mossblaser/lineOfLife/physical/base_axel.stl

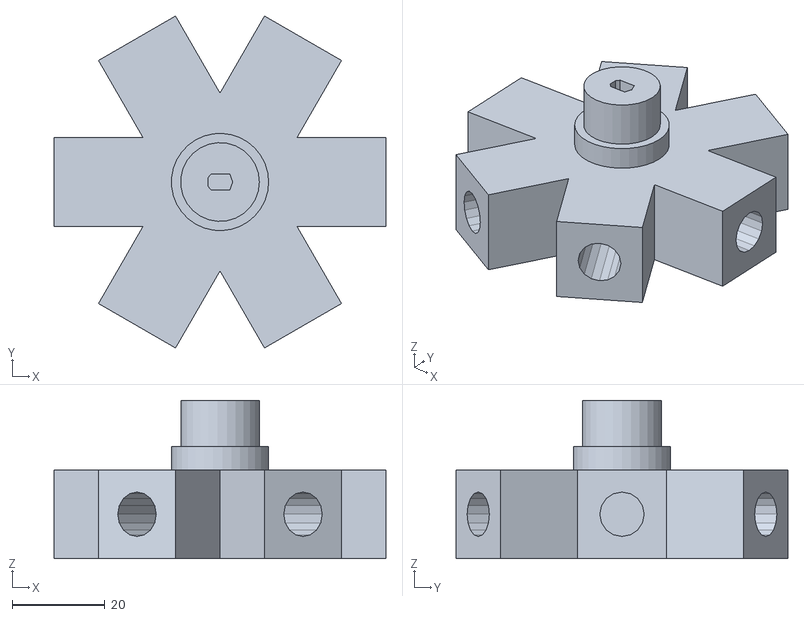
[picture p15: CAD file, 2014-01-31]
physical/base_axel.stl
71.7 x 71.7 x 34.2
