mossblaser/lineOfLife/controller/error_bitmap.h

{0x00,0x00,0x00,0x00,0x00,0x00,0x00,0x00,0x00,0x00,0x00,0x00,0x00,0x00,0x00},
{0x00,0x00,0x00,0x00,0x00,0x00,0x00,0x00,0x00,0x00,0x00,0x00,0x00,0x00,0x00},
{0x00,0x00,0x00,0x00,0x00,0x00,0x00,0x00,0x00,0x00,0x00,0xFC,0xFF,0x3F,0x00},
{0x00,0x00,0x00,0x00,0x00,0x00,0x00,0x00,0x00,0x00,0x00,0xFC,0xFF,0x3F,0x00},
{0x00,0x00,0x00,0x00,0x00,0x00,0x00,0x00,0x00,0x00,0x00,0xFC,0xFF,0x3F,0x00},
{0x00,0x00,0x00,0x00,0x00,0x00,0x00,0x00,0x00,0x00,0x00,0xFC,0xFF,0x3F,0x00},
{0x00,0x80,0xFF,0xFF,0x07,0x00,0x00,0x00,0x00,0x00,0x00,0xFC,0xFF,0x3F,0x00},
{0x00,0x80,0xFF,0xFF,0x07,0x00,0x00,0x00,0x00,0x00,0x00,0x3C,0x00,0x00,0x00},
{0x00,0x80,0xFF,0xFF,0x07,0x00,0x00,0x00,0x00,0x00,0x00,0x3C,0x00,0x00,0x00},
{0x00,0x80,0xFF,0xFF,0x07,0x00,0x00,0x00,0x00,0x00,0x00,0x3C,0x00,0x00,0x00},
{0x00,0x80,0xFF,0xFF,0x07,0x00,0x00,0x00,0x00,0x00,0x00,0x3C,0x00,0x00,0x00},
{0x00,0x80,0x07,0x00,0x00,0x00,0x00,0x00,0x00,0x00,0x00,0x3C,0x00,0x00,0x00},
{0x00,0x80,0x07,0x00,0x00,0x00,0x00,0x00,0x00,0x00,0x00,0x3C,0x00,0x00,0x00},
{0x00,0x80,0x07,0x00,0x00,0x00,0x00,0x00,0x00,0x00,0x00,0x3C,0x00,0x00,0x00},
{0x00,0x80,0x07,0x00,0x00,0x00,0x00,0x00,0x00,0x00,0x00,0x3C,0x00,0x00,0x00},
{0x00,0x80,0x07,0x00,0x00,0x00,0x00,0x00,0x00,0x00,0x00,0x00,0x00,0x00,0x00},
{0x00,0x80,0x07,0x00,0x00,0x00,0x00,0x3C,0x00,0x00,0x00,0x00,0x00,0x00,0x00},
{0x00,0x80,0x07,0x00,0x00,0x00,0x80,0xFF,0x00,0x00,0x00,0x00,0x00,0x00,0x00},
{0x00,0x80,0x07,0x00,0x00,0x00,0xC0,0xFF,0x01,0x00,0x00,0xFC,0xFF,0x38,0x00},
{0x00,0x00,0x00,0x00,0x00,0x00,0xE0,0xFF,0x03,0x00,0x00,0xFC,0xFF,0x7C,0x00},
{0x00,0x00,0x00,0x00,0x00,0x00,0xE0,0xFF,0x07,0x00,0x00,0xFC,0xFF,0x7C,0x00},
{0x00,0x80,0xFF,0x1F,0x02,0x00,0xE0,0x81,0x07,0x00,0x00,0xFC,0xFF,0x38,0x00},
{0x00,0x80,0xFF,0x3F,0x0F,0x00,0xF0,0x00,0x07,0x00,0x00,0x00,0x00,0x00,0x00},
{0x00,0x80,0xFF,0x3F,0x0F,0x00,0xF0,0x00,0x07,0x00,0x00,0x00,0x00,0x00,0x00},
{0x00,0x80,0xFF,0x3F,0x0F,0x00,0xF0,0x00,0x07,0x00,0x00,0x00,0x00,0x00,0x00},
{0x00,0x80,0xFF,0x3F,0x07,0x00,0xF0,0x00,0x07,0x00,0x00,0x00,0x00,0x00,0x00},
{0x00,0x00,0x00,0x00,0x00,0x00,0xE0,0xE7,0x07,0x00,0x00,0xFC,0xFF,0x00,0x00},
{0x00,0x00,0x00,0x00,0x00,0x00,0xE0,0xFF,0x07,0x00,0x00,0xFC,0xFF,0x00,0x00},
{0x00,0x00,0x00,0x3C,0x00,0x00,0xC0,0xFF,0x03,0x00,0x00,0xFC,0xFF,0x00,0x00},
{0x00,0x00,0x00,0x3C,0x00,0x00,0x80,0xFF,0x01,0x00,0x00,0xFC,0xFF,0x00,0x00},
{0x00,0x80,0xFF,0xFF,0x00,0x00,0x00,0xFF,0x00,0x00,0x00,0x00,0x78,0x00,0x00},
{0x00,0x80,0xFF,0xFF,0x03,0x00,0x00,0x00,0x00,0x00,0x00,0x00,0xF0,0x00,0x00},
{0x00,0x80,0xFF,0xFF,0x07,0x00,0x00,0x00,0x00,0x00,0x00,0x00,0xE0,0x00,0x00},
{0x00,0x80,0xFF,0xFF,0x0F,0x00,0x00,0x00,0x07,0x00,0x00,0x00,0xE0,0x00,0x00},
{0x00,0x80,0xFF,0xFF,0x0F,0x00,0x00,0x00,0x07,0x00,0x00,0x00,0xF0,0x01,0x00},
{0x00,0x00,0x00,0x3C,0x1F,0x00,0xF0,0xFF,0x7F,0x00,0x00,0xFC,0xFF,0x01,0x00},
{0x00,0x00,0x00,0x3C,0x1E,0x00,0xF0,0xFF,0xFF,0x00,0x00,0xFC,0xFF,0x00,0x00},
{0x00,0x00,0x00,0x18,0x0E,0x00,0xF0,0xFF,0xFF,0x01,0x00,0xFC,0xFF,0x00,0x00},
{0x00,0x00,0x00,0x00,0x00,0x00,0xF0,0xFF,0xFF,0x03,0x00,0xFC,0x7F,0x00,0x00},
{0x00,0x00,0xF8,0x01,0x00,0x00,0x00,0x80,0xF7,0x03,0x00,0xFC,0x0F,0x00,0x00},
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
