mossblaser/lineOfLife/controller/number_bitmaps.h

{
	0x1C, //   111   
	0x22, //  1   1  
	0x32, //  1  11  
	0x2A, //  1 1 1  
	0x26, //  11  1  
	0x22, //  1   1  
	0x1C, //   111   
	0x00, //         
},
{
	0x08, //    1    
	0x0C, //   11    
	0x08, //    1    
	0x08, //    1    
	0x08, //    1    
	0x08, //    1    
	0x1C, //   111   
	0x00, //         
},
{
	0x1C, //   111   
	0x22, //  1   1  
	0x20, //      1  
	0x10, //     1   
	0x08, //    1    
	0x04, //   1     
	0x3E, //  11111  
	0x00, //         
},
{
	0x3E, //  11111  
	0x10, //     1   
	0x08, //    1    
	0x10, //     1   
	0x20, //      1  
	0x22, //  1   1  
	0x1C, //   111   
	0x00, //         
},
{
	0x10, //     1   
	0x18, //    11   
	0x14, //   1 1   
	0x12, //  1  1   
	0x3E, //  11111  
	0x10, //     1   
	0x10, //     1   
	0x00, //         
},
{
	0x3E, //  11111  
	0x02, //  1      
	0x1E, //  1111   
	0x20, //      1  
	0x20, //      1  
	0x22, //  1   1  
	0x1C, //   111   
	0x00, //         
},
{
	0x18, //    11   
	0x04, //   1     
	0x02, //  1      
	0x1E, //  1111   
	0x22, //  1   1  
	0x22, //  1   1  
	0x1C, //   111   
	0x00, //         
},
{
	0x3E, //  11111  
	0x20, //      1  
	0x10, //     1   
	0x08, //    1    
	0x04, //   1     
	0x04, //   1     
	0x04, //   1     
	0x00, //         
},
{
	0x1C, //   111   
	0x22, //  1   1  
	0x22, //  1   1  
	0x1C, //   111   
	0x22, //  1   1  
	0x22, //  1   1  
	0x1C, //   111   
	0x00, //         
},
{
	0x1C, //   111   
	0x22, //  1   1  
	0x22, //  1   1  
	0x3C, //   1111  
	0x20, //      1  
	0x10, //     1   
	0x0C, //   11    
	0x00, //         
},
