mossblaser/lineOfLife/controller/presenting_bitmap.h

0x78,0x00,0x00,0x00,0x00,0x81,0x00,0x3C,0x00,0x00,0x0C,0x00,0x00,0x00,0x00, //    1111                                 1      1          1111                    11                                    
0x88,0x00,0x00,0x00,0x80,0x03,0x00,0x22,0x00,0x00,0x08,0x00,0x00,0x00,0x00, //    1   1                               111               1   1                     1                                    
0x88,0x1A,0xC7,0x73,0x1A,0xC1,0x68,0x22,0xA0,0x89,0x08,0x07,0x00,0x00,0x00, //    1   1 1 11   111   1111  111  1 11   1     11   1 11  1   1       1 11  1   1   1    111                             
0x78,0xA6,0x28,0x88,0x26,0x81,0x98,0x3C,0x60,0x8A,0x88,0x08,0x00,0x00,0x00, //    1111  11  1 1   1 1     1   1 11  1  1      1   11  1  1111       11  1 1   1   1   1   1                            
0x08,0x82,0xCF,0xF9,0x22,0x81,0x88,0x20,0x20,0x88,0x88,0x0F,0x00,0x00,0x00, //    1     1     11111  111  11111 1   1  1      1   1   1     1       1     1   1   1   11111                            
0x08,0x82,0x00,0x0A,0x22,0x89,0x88,0x20,0x20,0xC8,0x88,0x00,0x00,0x00,0x00, //    1     1     1         1 1     1   1  1  1   1   1   1     1       1     1  11   1   1                                
0x08,0x02,0xE7,0x71,0x22,0xC6,0x89,0x1C,0x20,0xB0,0x1C,0x07,0x00,0x00,0x00, //    1     1      111  1111   111  1   1   11   111  1   1  111        1      11 1  111   111                             
0x00,0x00,0x00,0x00,0x00,0x00,0x00,0x00,0x00,0x00,0x00,0x00,0x00,0x00,0x00, //                                                                                                                         
