mossblaser/lineOfLife/python/examples/cellular_automata.py

#!/usr/bin/env python

"""
A quick-and-dirty 1D cellular automata demo. Displays randomly initialised
automata with random rules. If rules are supplied as arguments, the displayed
rules will be selected from the supplied list of rules.

See http://en.wikipedia.org/wiki/Elementary_cellular_automaton for more details
of this class of automata.
"""

import sys
import serial
import random
import time

from line_of_life.driver import LineOfLife
from line_of_life.bitmap import text_to_lol

# Connect to the display
ser = serial.Serial(port = "/dev/ttyUSB0", baudrate = 115200, timeout = 3)
time.sleep(3)
lol = LineOfLife(ser)

# Clear the display's current buffer to start displaying the new automata
# immediately.
lol.clear_buffer()

lol.pixel_aspect_ratio = 1
lol.pixel_duty = 1.0

# A mask for the bits representing the cells of the automata
mask = (1l<<lol.display_height)-1

while True:
	# Pick a random rule to show, or one selected on the command line
	if len(sys.argv) > 1:
		rule = random.choice(map(int, sys.argv[1:]))
	else:
		rule = int(random.random()*0xFF)
	
	# Announce the automata
	for line in text_to_lol("Presenting Rule %d"%rule, lol.display_height, rotate=True):
		lol.push_line(line)
	lol.push_line([0] * lol.display_height)
	
	# Pick randomly between a random initial state and a single seed pixel
	if random.random() < 0.5:
		state = sum(1l<<n for n in range(lol.display_height) if random.random()<0.5)
	else:
		state = 1<<(lol.display_height/2)
	
	# Run this automata for one quarter of a rotation
	for _ in range(lol.display_width/2):
		# Calculate the new automata state
		new_state = 0l
		state <<= 1
		for bit_num in range(1, lol.display_height+1):
			new_state |= ((rule>>((state>>(bit_num-1))&0b111))&1)<<(bit_num-1)
		
		# Move on to another automata immediately if this one doesn't change
		if (state>>1) == new_state&mask:
			break
		
		state = new_state&mask
		
		# Push the line to the display
		lol.push_line([state&(1<<y) for y in range(lol.display_height)])
	
	# Put a blank space between different automata
	for _ in range(5):
		lol.push_line([0] * lol.display_height)
